bt-soft/pico-radio-9/include/defines.h

/*
 * Project: [pico-radio-9] Raspberry Pi Pico Si4735 Radio                                                              *
 * File: defines.h                                                                                                     *
 * Created Date: 2025.11.07.                                                                                           *
 *                                                                                                                     *
 * Author: BT-Soft                                                                                                     *
 * GitHub: https://github.com/bt-soft                                                                                  *
 * Blog: https://electrodiy.blog.hu/                                                                                   *
 * -----                                                                                                               *
 * Copyright (c) 2025 BT-Soft                                                                                          *
 * License: MIT License                                                                                                *
 * 	Bárki szabadon használhatja, módosíthatja, terjeszthet, beépítheti más                                             *
 * 	projektbe (akár zártkódúba is), akár pénzt is kereshet vele                                                        *
 * 	Egyetlen feltétel:                                                                                                 *
 * 		a licencet és a szerző nevét meg kell tartani a forrásban!                                                     *
 * -----                                                                                                               *
 * Last Modified: 2025.11.30, Sunday  12:16:19                                                                         *
 * Modified By: BT-Soft                                                                                                *
 * -----                                                                                                               *
 * HISTORY:                                                                                                            *
 * Date      	By	Comments                                                                                           *
 * ----------	---	-------------------------------------------------------------------------------------------------  *
 */

#pragma once

#include <Arduino.h>

#include "pins.h"

//---- Program Information ------------------------------------------

#define PROGRAM_NAME "Pico Radio v9"
#define PROGRAM_VERSION "0.0.9"
#define PROGRAM_AUTHOR "bt-soft (2025)"

//---- Program Information ------------------------------------------

//--- ScreenNames ----
#define SCREEN_NAME_FM "ScreenFM"
#define SCREEN_NAME_AM "ScreenAM"
#define SCREEN_NAME_SCREENSAVER "SaverScreen"
#define SCREEN_NAME_SETUP "ScreenSetup"
#define SCREEN_NAME_SETUP_SYSTEM "ScreenSetupSystem"
#define SCREEN_NAME_SETUP_SI4735 "ScreenSetupSi4735"
#define SCREEN_NAME_SETUP_AUDIO_PROC "ScreenSetupAudioProc"
#define SCREEN_NAME_CW_RTTY "ScreenCwRtty"

#define SCREEN_NAME_MEMORY "ScreenMemory"
#define SCREEN_NAME_SCAN "ScreenScan"

#define SCREEN_NAME_DECODER_CW "ScreenCwDecoder"
#define SCREEN_NAME_DECODER_RTTY "ScreenRttyDecoder"
#define SCREEN_NAME_DECODER_SSTV "ScreenSstvDecoder"
#define SCREEN_NAME_DECODER_WEFAX "ScreenWefaxDecoder"

#define SCREEN_NAME_TEST "TestScreen"
#define SCREEN_NAME_EMPTY "EmptyScreen"

//--- Debug ---
#define __DEBUG // Debug mód vezérlése

// Debug keretek rajzolása a UI komponensek köré
// #define DRAW_DEBUG_GUI_FRAMES

//--- Debug ---
#ifdef __DEBUG
#define DEBUG(fmt, ...) Serial.printf(fmt __VA_OPT__(, ) __VA_ARGS__)
#else
#define DEBUG(fmt, ...) // Üres makró, ha __DEBUG nincs definiálva
#endif

//--- Radio EEPROM Size ---
#define RADIO_EEPROM_SIZE_IN_KB 3 // EEPROM méret KB-ban (512-4096 között módosítható)

// Rotary Encoder
#define __USE_ROTARY_ENCODER_IN_HW_TIMER

// TFT háttérvilágítás max érték
#define TFT_BACKGROUND_LED_MAX_BRIGHTNESS 255
#define TFT_BACKGROUND_LED_MIN_BRIGHTNESS 5

//--- Battery ---
#define MIN_BATTERY_VOLTAGE 270 // Minimum akkumulátor feszültség (V*100)
#define MAX_BATTERY_VOLTAGE 405 // Maximum akkumulátor feszültség (V*100)

//--- ScreenSaver
#define SCREEN_SAVER_TIMEOUT_MIN 1
#define SCREEN_SAVER_TIMEOUT_MAX 60
#define SCREEN_SAVER_TIMEOUT 10 // 1 perc a képernyővédő időzítése - tesztelés

//--- Array Utils ---
#define ARRAY_ITEM_COUNT(array) (sizeof(array) / sizeof(array[0]))

//--- Band Table ---
#define BANDTABLE_SIZE 30 // A band tábla mérete (bandTable[] tömb)

//--- C String compare -----
#define STREQ(a, b) (strcmp((a), (b)) == 0)

#define SPECTRUM_GAIN_MODE_AUTO ((int8_t)-128)        // Auto Gain mód spektrum vizualizációhoz (int8_t sentinel)
#define SPECTRUM_GAIN_MODE_MANUAL_DEFAULT ((int8_t)0) // Manual Gain mód alapértelmezett érték spektrum vizualizációhoz (0 dB)

#define MIN_AUDIO_FREQUENCY_HZ 300   // Minimum audio frekvencia (Hz)
#define MAX_AUDIO_FREQUENCY_HZ 15000 // Maximum audio frekvencia (Hz)

#define LINEAR_TO_DECIBELL(x) (20.0f * log10f(x)) // Lineáris érték dB-be konvertálása
